trteodor/Line_Follower_STM32H7/Pictures/20210125_161238.jpg

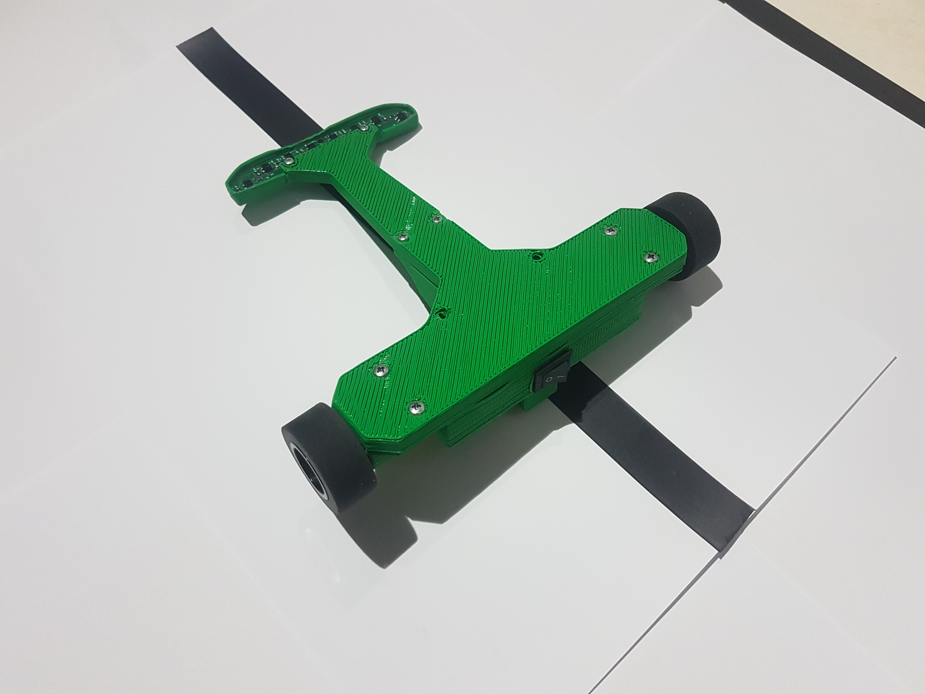
Pictures/20210125_161238.jpg
